InnoBox4/Packlock-Smart-Kotak-Paket-Berbais-IoT/DOKUMENTASI/Hasil Jadi.jpg

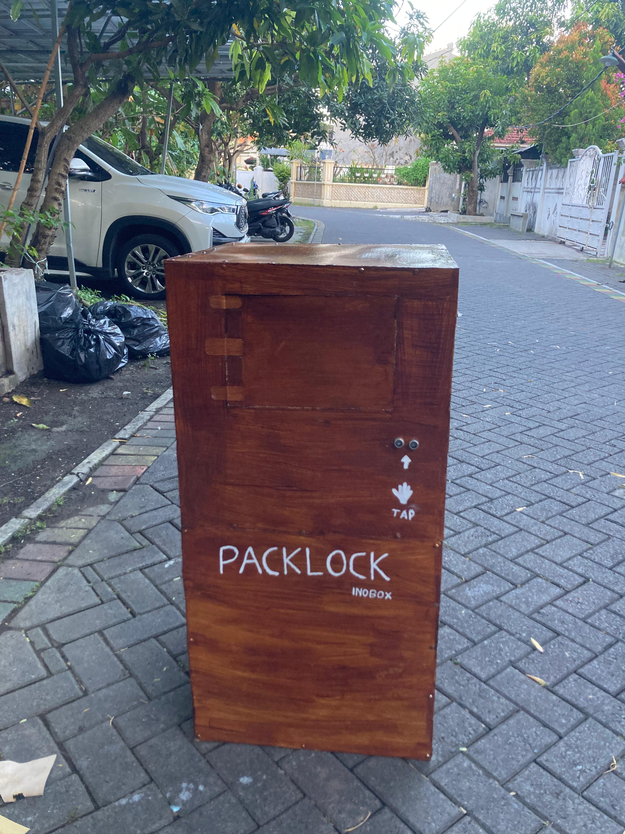
DOKUMENTASI/Hasil Jadi.jpg
