InnoBox4/Packlock-Smart-Kotak-Paket-Berbais-IoT/DOKUMENTASI/Kerangka sebelum di cat.jpg

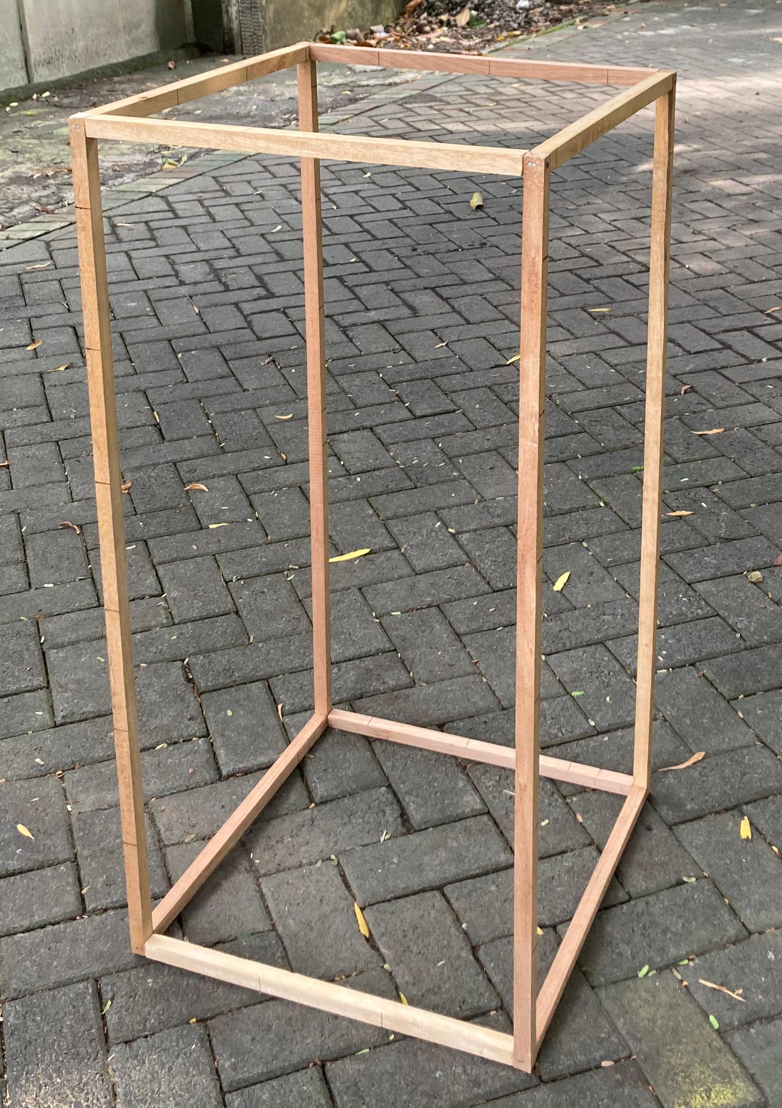
DOKUMENTASI/Kerangka sebelum di cat.jpg
