InnoBox4/Packlock-Smart-Kotak-Paket-Berbais-IoT/DOKUMENTASI/Kerangka setelah di cat.jpg

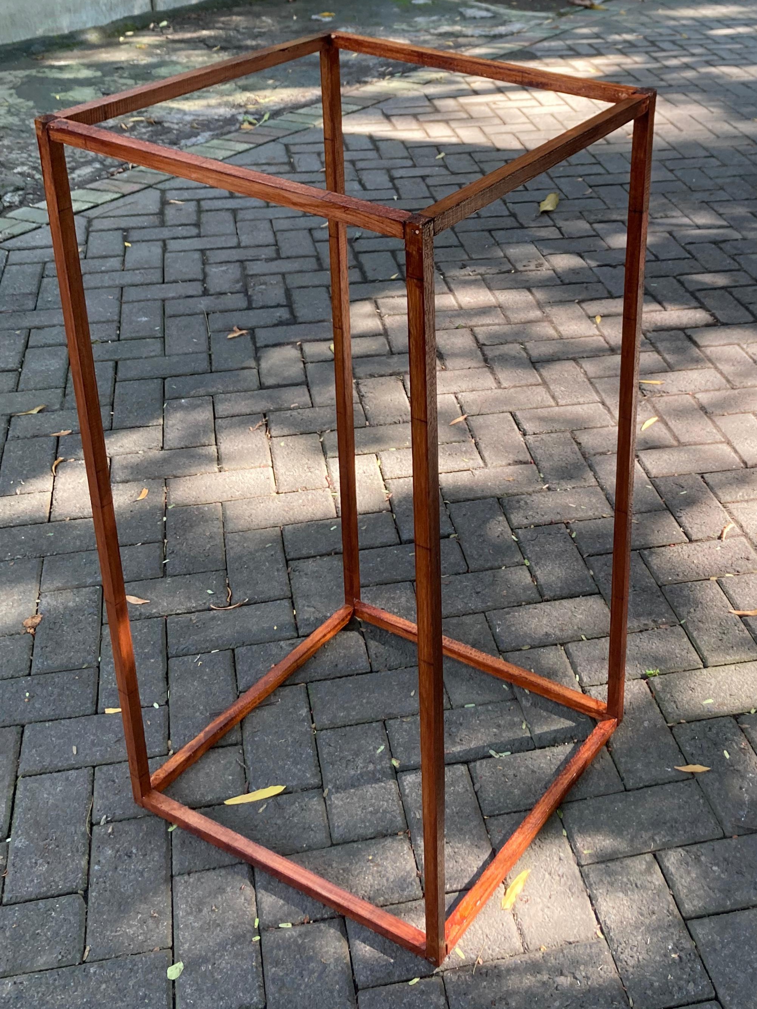
DOKUMENTASI/Kerangka setelah di cat.jpg
