InnoBox4/Packlock-Smart-Kotak-Paket-Berbais-IoT/DOKUMENTASI/membuat kerangka.jpg

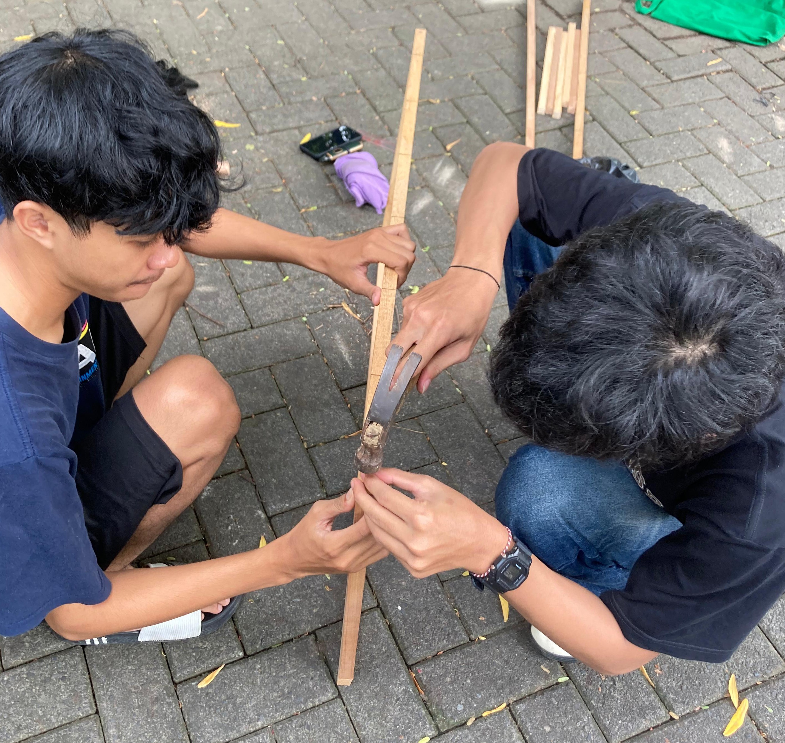
DOKUMENTASI/membuat kerangka.jpg
