InnoBox4/Packlock-Smart-Kotak-Paket-Berbais-IoT/DOKUMENTASI/Pembuatan Obstekel.jpg

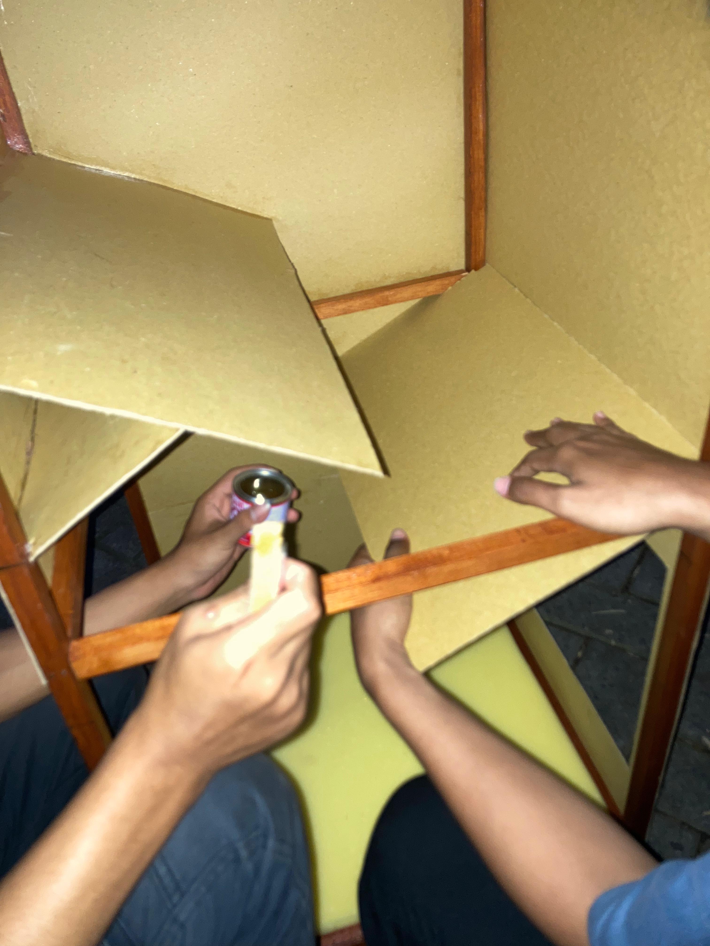
DOKUMENTASI/Pembuatan Obstekel.jpg
