InnoBox4/Packlock-Smart-Kotak-Paket-Berbais-IoT/DOKUMENTASI/Pemotongan Karton.jpg

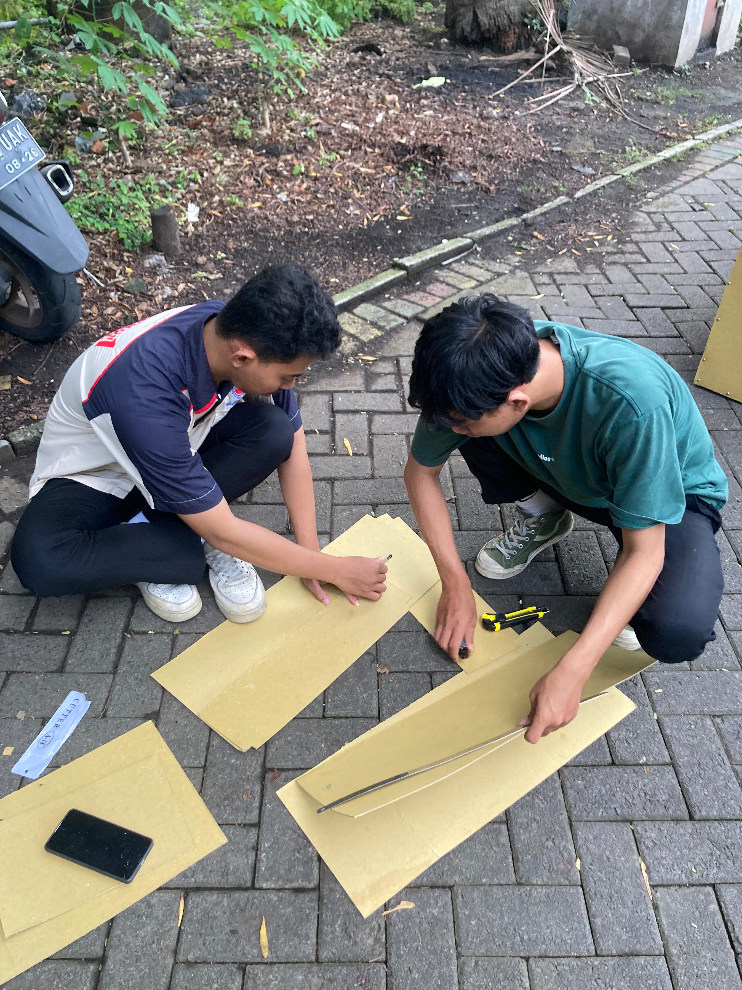
DOKUMENTASI/Pemotongan Karton.jpg
