InnoBox4/Packlock-Smart-Kotak-Paket-Berbais-IoT/DOKUMENTASI/Proses pelapisan .jpg

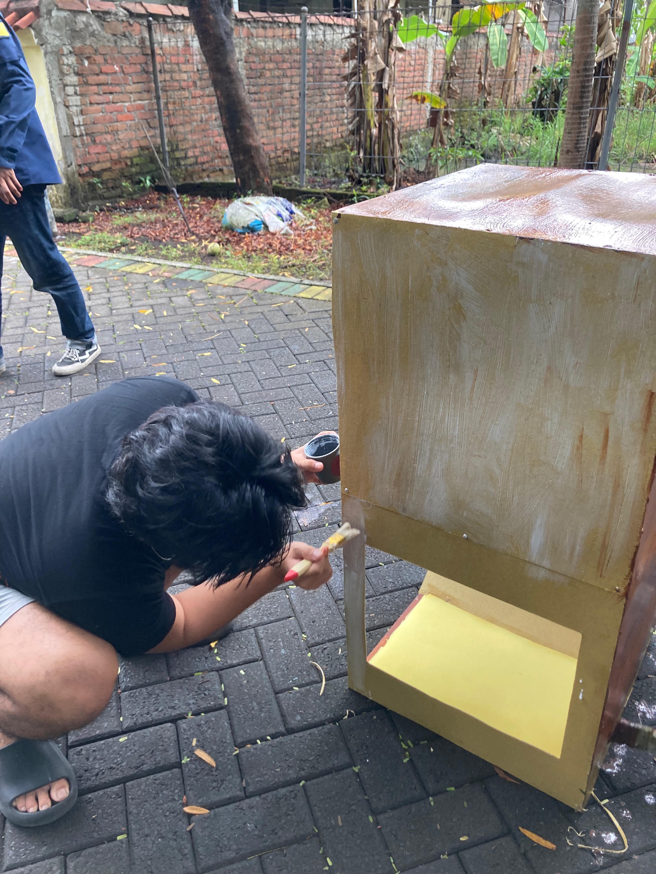
DOKUMENTASI/Proses pelapisan .jpg
