InnoBox4/Packlock-Smart-Kotak-Paket-Berbais-IoT/DOKUMENTASI/Proses pemotongan karton.jpg

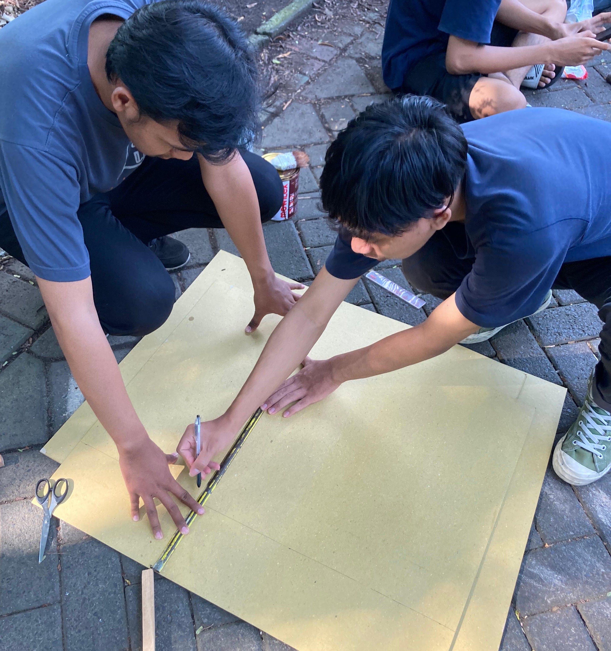
DOKUMENTASI/Proses pemotongan karton.jpg
