InnoBox4/Packlock-Smart-Kotak-Paket-Berbais-IoT/DOKUMENTASI/proses pemotongan kayu.jpg

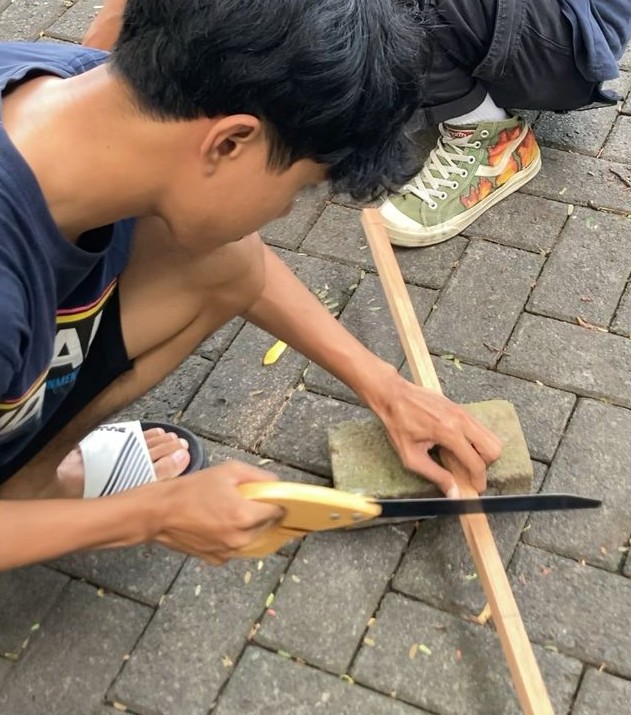
DOKUMENTASI/proses pemotongan kayu.jpg
