InnoBox4/Packlock-Smart-Kotak-Paket-Berbais-IoT/DOKUMENTASI/Proses Pengecatan.jpg

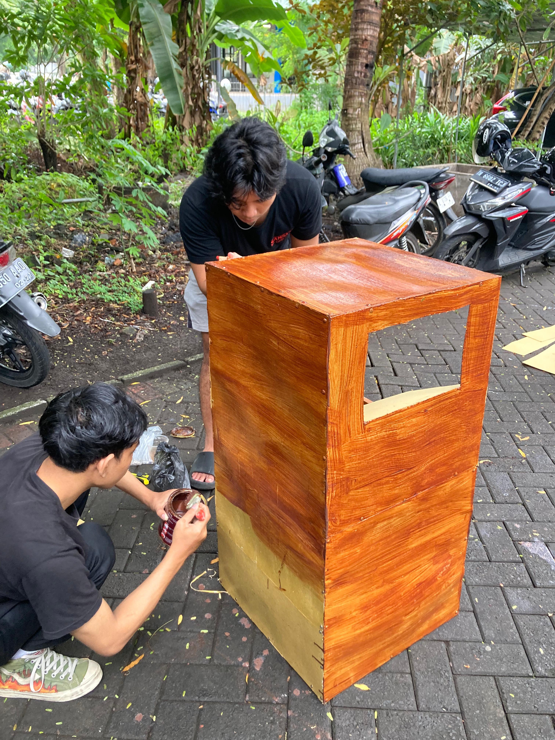
DOKUMENTASI/Proses Pengecatan.jpg
