InnoBox4/Packlock-Smart-Kotak-Paket-Berbais-IoT/DOKUMENTASI/Proses Setengah jadi.jpg

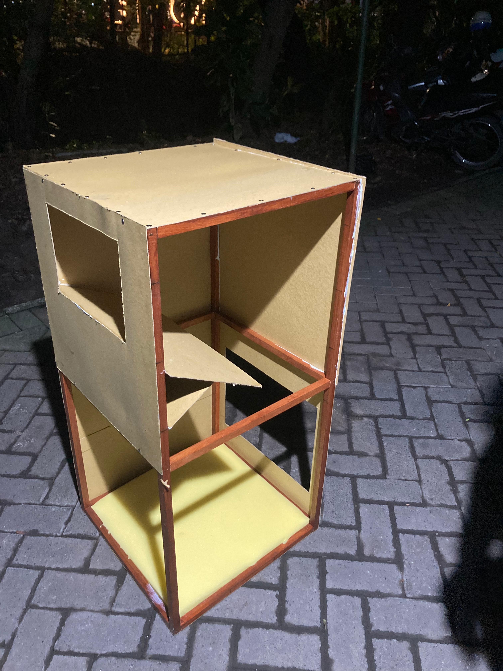
DOKUMENTASI/Proses Setengah jadi.jpg
