InnoBox4/Packlock-Smart-Kotak-Paket-Berbais-IoT/DOKUMENTASI/Tampak Halang rintang.jpg

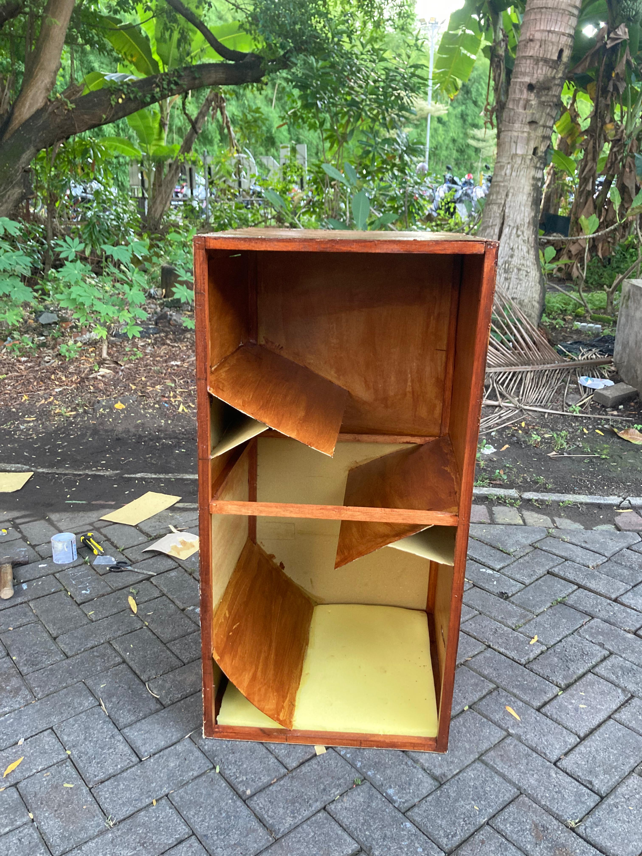
DOKUMENTASI/Tampak Halang rintang.jpg
