InnoBox4/Packlock-Smart-Kotak-Paket-Berbais-IoT/PROGRAM/Gambar_Simulasi_Kontrol_Pintu.jpg

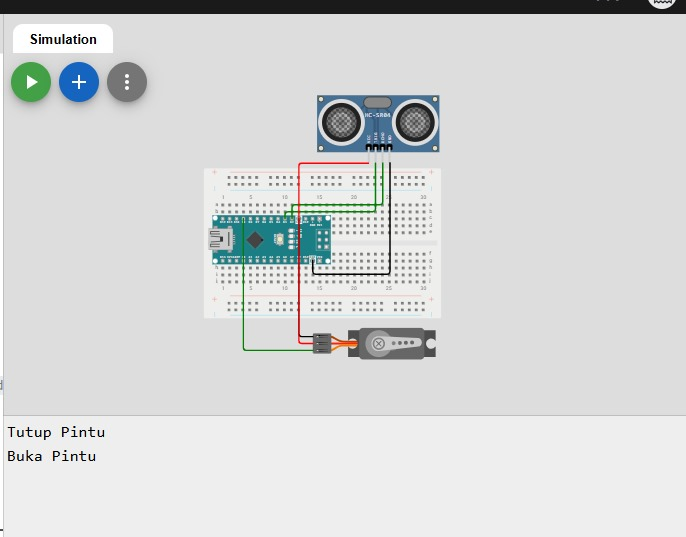
PROGRAM/Gambar_Simulasi_Kontrol_Pintu.jpg
